stevenchadburrow/AcolyteHandPICd/test.c

/******************************************************************************/
/* Files to Include                                                           */
/******************************************************************************/


// #pragma config statements should precede project file includes.
// Use project enums instead of #define for ON and OFF.


#if defined(__XC)
    #include <xc.h>        /* XC8 General Include File */
#elif defined(HI_TECH_C)
    #include <htc.h>       /* HiTech General Include File */
#elif defined(__18CXX)
    #include <p18cxxx.h>   /* C18 General Include File */
#endif

#if defined(__XC) || defined(HI_TECH_C)

#include <stdint.h>        /* For uint8_t definition */
#include <stdbool.h>       /* For true/false definition */

#endif

#include "system.h"        /* System funct/params, like osc/peripheral config */
#include "user.h"          /* User funct/params, such as InitApp */


/******************************************************************************/
/* User Global Variable Declaration                                           */
/******************************************************************************/

/* i.e. uint8_t <variable_name>; */

/******************************************************************************/
/* Main Program                                                               */
/******************************************************************************/


unsigned int readjoy()
{ 
	volatile unsigned char joy_a = 0xFF;
	volatile unsigned char joy_b = 0xFF;
	volatile unsigned char i;
	volatile unsigned int both;
	
	// only changes joy_a at this point!!!
  
	TRISB = 0xF0;
	TRISB = 0xF0;
	//TRISB = 0xE0;
	//TRISB = 0xE0;
	LATB = 0x03;
	LATB = 0x03;
	LATB = 0x07; // might interfere with TX/RX???
	LATB = 0x07;
	LATB = 0x03;
	LATB = 0x03;
	LATB = 0x0B;
	LATB = 0x0B;
	
	for (i=0x00; i<0x06; i++)
	{
		joy_a = joy_a << 1;
		if (RB5 != 0) joy_a = joy_a | 0x01;
		LATB = 0x0F;
		LATB = 0x0F;
		LATB = 0x0B;
		LATB = 0x0B;
	}
	
	for (i=0x00; i<0x06; i++)
	{
		joy_b = joy_b << 1;
		if (RB5 != 0) joy_b = joy_b | 0x01;
		LATB = 0x0F;
		LATB = 0x0F;
		LATB = 0x0B;
		LATB = 0x0B;
	}

	TRISB = 0xE0;
	TRISB = 0xE0;
	//TRISB = 0xF0;
	//TRISB = 0xF0;
	LATB = 0x03;
	LATB = 0x03;
	LATB = 0x07;
	LATB = 0x07;
	LATB = 0x03;
	LATB = 0x03;
	LATB = 0x0B;
	LATB = 0x0B;
	
	for (i=0x00; i<0x04; i++)
	{
		LATB = 0x0F;
		LATB = 0x0F;
		LATB = 0x0B;
		LATB = 0x0B;
	}
	
	for (i=0x00; i<0x02; i++)
	{
		joy_a = joy_a << 1;
		if (RB5 != 0) joy_a = joy_a | 0x01;
		LATB = 0x0F;
		LATB = 0x0F;
		LATB = 0x0B;
		LATB = 0x0B;
	}
	
	for (i=0x00; i<0x04; i++)
	{
		LATB = 0x0F;
		LATB = 0x0F;
		LATB = 0x0B;
		LATB = 0x0B;
	}
	
	for (i=0x00; i<0x02; i++)
	{
		joy_b = joy_b << 1;
		if (RB5 != 0) joy_b = joy_b | 0x01;
		LATB = 0x0F;
		LATB = 0x0F;
		LATB = 0x0B;
		LATB = 0x0B;
	}
	
	TRISB = 0xF0;
	TRISB = 0xF0;
	//TRISB = 0xE0;
	//TRISB = 0xE0;
	LATB = 0x03;
	LATB = 0x03;
	
	both = ((unsigned int)(joy_a) << 8) + (unsigned int)(joy_b);
	
	return both;
};

char receivechar(void)
{
	while (RCIF == 0) { } // wait to receive character
	RCIF = 0; // clear flag

	return RCREG;
};

void transmitchar(char value)
{
	while (TXIF == 0) { } // wait to transmit character
	TXIF = 0; // clear flag

	TXREG = value;
};

void highaddr(unsigned char value)
{
	PORTC = value;
	PORTB = 0x01;
	PORTB = 0x03;
};

void lowaddr(unsigned char value)
{
	PORTC = value;
};

void writedata(unsigned char value)
{
	PMDOUT1L = value;
	PORTB = 0x02;
	PORTB = 0x03;
};

unsigned char readdata() // requires highaddr() afterwards
{ 
    PMSTATH = 0x00;
	PORTB = 0x01;
	PORTB = 0x00;
	PORTB = 0x01;
	PORTB = 0x01; // needs a second for delay purposes
	return PMDIN1L;
};

const unsigned char bitmap[2048] = {
	0x00,0x00,0x00,0x00,0x00,0x00,0x00,0x00,
	0x00,0x00,0x00,0x00,0x00,0x00,0x00,0x00,
	0x00,0x00,0x00,0x00,0x00,0x00,0x00,0x00,
	0x00,0x00,0x00,0x00,0x00,0x00,0x00,0x00,
	0x00,0x00,0x00,0x00,0x00,0x00,0x00,0x00,
	0x00,0x00,0x00,0x00,0x00,0x00,0x00,0x00,
	0x00,0x00,0x00,0x00,0x00,0x00,0x00,0x00,
	0x00,0x00,0x00,0x00,0x00,0x00,0x00,0x00,
	0x00,0x00,0x00,0x00,0x00,0x00,0x00,0x00,
	0x00,0x00,0x00,0x00,0x00,0x00,0x00,0x00,
	0x00,0x00,0x00,0x00,0x00,0x00,0x00,0x00,
	0x00,0x00,0x00,0x00,0x00,0x00,0x00,0x00,
	0x00,0x00,0x00,0x00,0x00,0x00,0x00,0x00,
	0x00,0x00,0x00,0x00,0x00,0x00,0x00,0x00,
	0x00,0x00,0x00,0x00,0x00,0x00,0x00,0x00,
	0x00,0x00,0x00,0x00,0x00,0x00,0x00,0x00,
	0x00,0x00,0x00,0x00,0x00,0x00,0x00,0x00,
	0x00,0x00,0x00,0x00,0x00,0x00,0x00,0x00,
	0x00,0x00,0x00,0x00,0x00,0x00,0x00,0x00,
	0x00,0x00,0x00,0x00,0x00,0x00,0x00,0x00,
	0x00,0x00,0x00,0x00,0x00,0x00,0x00,0x00,
	0x00,0x00,0x00,0x00,0x00,0x00,0x00,0x00,
	0x00,0x00,0x00,0x00,0x00,0x00,0x00,0x00,
	0x00,0x00,0x00,0x00,0x00,0x00,0x00,0x00,
	0x00,0x00,0x00,0x00,0x00,0x00,0x00,0x00,
	0x00,0x00,0x00,0x00,0x00,0x00,0x00,0x00,
	0x00,0x00,0x00,0x00,0x00,0x00,0x00,0x00,
	0x00,0x00,0x00,0x00,0x00,0x00,0x00,0x00,
	0x00,0x00,0x00,0x00,0x00,0x00,0x00,0x00,
	0x00,0x00,0x00,0x00,0x00,0x00,0x00,0x00,
	0x00,0x00,0x00,0x00,0x00,0x00,0x00,0x00,
	0x00,0x00,0x00,0x00,0x00,0x00,0x00,0x00,
	0x00,0x00,0x00,0x00,0x00,0x00,0x00,0x00,
	0x00,0x00,0x00,0x00,0x00,0x00,0x00,0x00,
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
	0x5D,0x75,0x54,0x75,0xD7,0x77,0x77,0xFF,
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
};

void main(void)
{
	
    /* Configure the oscillator for the device */
    ConfigureOscillator();

    /* Initialize I/O and Peripherals for application */
    InitApp();

    /* TODO <INSERT USER APPLICATION CODE HERE> */

	// turn PLL on
	//PLLEN = 1;
	
	__delay_ms(1000); // delay at beginning until everything is stabilized
	
	// setup initial tri-state and output levels
	PORTA = 0x00;
	LATA = 0x00;
    TRISA = 0x00;
	PORTB = 0x03;
	LATB = 0x00;
	TRISB = 0xF0;
	PORTC = 0x00;
	LATC = 0x00;
	TRISC = 0x00;
	PORTD = 0x00;
	LATD = 0x00;
	TRISD = 0xFF;
	PORTE = 0x00;
	LATE = 0x00;
	TRISE = 0x0F; // 0xFF or 0xF0
	
	// disable interrupts
	INTCON = 0x00;
	INTCON2 = 0x80;
	INTCON3 = 0x00;
	PIE1 = 0x00;
	PIE2 = 0x00;
	PIE3 = 0x00;
	PIE4 = 0x00;
	PIE5 = 0x00;
	
	// disable analog for digital I/O
	ANCON0 = 0xFF;
	ANCON1 = 0x1F;
	
	// disable open drain and use TTL on PMP
	ODCON1 = 0x00;
	ODCON2 = 0x00;
	ODCON3 = 0x00;
	PADCFG1 = 0x05; // 0x04 or 0x05
	
	// setup Parallel Master/Slave Port
	PMCONH = 0x00; // disable everything
	PMCONL = 0x0C; // 0x0C or 0x04, low-enable
	PMMODEH = 0x00; 
	PMMODEL = 0x00;
    
	PMEH = 0x00;
	PMEL = 0x00;
	PMADDRH = 0x40; // 0x00 or 0x40?
	PMADDRL = 0x00;
	PMSTATH = 0x00;
	PMSTATL = 0x00;
	
	PMCONH = 0x87; // 0x87, re-enable everything
	PMCONL = 0x84; // 0x80?
	
	// small examples
	//PMDOUT1L = 0x55; // output on data bus
	//PORTA = PMDIN1L; // input from data bus

	/*
	// setup TX/RX on RB6/RP9 and RB7/RP10 respectively
	RPOR10 = 0x06; // TX2 on RP9
	RPINR16 = 0x0A; // RX2 on RP10
	TRISB = TRISB | 0x80; // make sure RX is input
	TRISB = TRISB & 0x40; // make sure TX is output
	TXSTA1 = 0x04; // disable TX1
	RCSTA1 = 0x10; // disable RX1
	SPBRG2 = 41; // set for 6.28 MHz, 6293750 / (16 * (9600 + 1))
	SPBRGH2 = 0; // set to zero
	BAUDCON2 = 0x32; // stay in 8-bit mode, inverted
	TXSTA2 = 0x24; // 'high speed' transmit enabled
	RCSTA2 = 0x90; // serial port enabled, continuous receives
	RCIF = 0; // clear flag
	TXIF = 0; // clear flag
	*/
	
	
	volatile unsigned int i = 0, j = 0;
	volatile unsigned char x = 0;
	/*
	for (i=0; i<128; i++)
	{
		highaddr((unsigned char)(i));
		
		for (j=0; j<100; j++)
		{
			lowaddr((unsigned char)(j));
			writedata((unsigned char)(i) + (unsigned char)(j));
		}
		
		for (j=100; j<128; j++)
		{
			lowaddr((unsigned char)(j));
			writedata(0xB7);
		}
		
		for (j=128; j<200; j++)
		{
			lowaddr((unsigned char)(j));
			writedata((unsigned char)(i) + (unsigned char)(j));
		}
		
		for (j=200; j<256; j++)
		{
			lowaddr((unsigned char)(j));
			writedata(0xB7);
		}
	}
	*/
	
	for (i = 0x00; i<128; i++)
	{
		highaddr((unsigned char)i);
		
		for (j = 0x00; j<256; j++)
		{
			lowaddr((unsigned char)j);
			writedata(splash[(unsigned int)(i * 256 + j)]);
		}
	}
	
	display(0x00, 0x00, 'A');
	display(0x01, 0x00, 'c');
	display(0x02, 0x00, 'o');
	display(0x03, 0x00, 'l');
	display(0x04, 0x00, 'y');
	display(0x05, 0x00, 't');
	display(0x06, 0x00, 'e');
	display(0x07, 0x00, ' ');
	display(0x08, 0x00, '-');
	display(0x09, 0x00, ' ');
	display(0x0A, 0x00, 'H');
	display(0x0B, 0x00, 'a');
	display(0x0C, 0x00, 'n');
	display(0x0D, 0x00, 'd');
	display(0x0E, 0x00, ' ');
	display(0x0F, 0x00, 'P');
	display(0x10, 0x00, 'I');
	display(0x11, 0x00, 'C');
	display(0x12, 0x00, '\'');
	display(0x13, 0x00, 'd');
	
	/*
	highaddr(0x01);
	lowaddr(0x01);
	x = readdata();
	highaddr(0x01);
	lowaddr(0x01);
	x = readdata(); // reading twice seems to help
	hex(0x30, 0x01, x);
	*/
	
	/*
	for (i=0; i<16; i++)
	{
		for (j=0; j<50; j++)
		{
			display((unsigned char)(j), (unsigned char)(i), (unsigned char)(i+j+32));
		}
	}
	*/
	/*
	x = 0xC9;
	
	highaddr(0x01);
	lowaddr(0x01);
	writedata(x);
	highaddr(0x00);
	lowaddr(0x00);
	x = readdata();
	highaddr(0x00);
	lowaddr(0x01);
	writedata(x);
	*/
	/*
	for (i=0; i<16; i++)
	{
		for (j=0; j<64; j++)
		{
			highaddr((unsigned char)(i));
			lowaddr((unsigned char)(j));
			x = readdata();
			highaddr((unsigned char)(i+0x60));
			lowaddr((unsigned char)(j+0x08));
			writedata(x);
		}
		
		for (j=128; j<192; j++)
		{
			highaddr((unsigned char)(i));
			lowaddr((unsigned char)(j));
			x = readdata();
			highaddr((unsigned char)(i+0x60));
			lowaddr((unsigned char)(j+0x08));
			writedata(x);
		}
	}
	
	for (i=0; i<16; i++)
	{
		for (j=0; j<64; j++)
		{
			highaddr((unsigned char)(i+0x40));
			lowaddr((unsigned char)(j));
			x = readdata();
			highaddr((unsigned char)(i+0x20));
			lowaddr((unsigned char)(j+0x08));
			writedata(x);
		}
		
		for (j=128; j<192; j++)
		{
			highaddr((unsigned char)(i+0x40));
			lowaddr((unsigned char)(j));
			x = readdata();
			highaddr((unsigned char)(i+0x20));
			lowaddr((unsigned char)(j+0x08));
			writedata(x);
		}
	}
	*/
	/*
	x = 0x9C;
	
	highaddr(0x01);
	lowaddr(0x01);
	writedata(x);
	highaddr(0x00);
	lowaddr(0x00);
	x = readdata();
	highaddr(0x00);
	lowaddr(0x01);
	writedata(x);
	*/
/*	
	highaddr(0x00);
	lowaddr(0x00);
	writedata(0xA5);
	
	highaddr(0x01);
	lowaddr(0x01);
	writedata(0xC9);
	lowaddr(0x08);
	writedata(0x5A);
*/	
	
	
	//PMDIN1L = 0xA5;
	
	volatile unsigned int y = 0x0000;
	
	//LATB = PORTB | 0x10;

	while (1)
	{
		y = readjoy();
		
		hex(0x2E, 0x00, (unsigned char)((y & 0xFF00) >> 8));
		hex(0x30, 0x00, (unsigned char)(y & 0x00FF));
		
		__delay_ms(100);
	}


}
